benklop/esp8266-2-relay-box/project_box_001.png

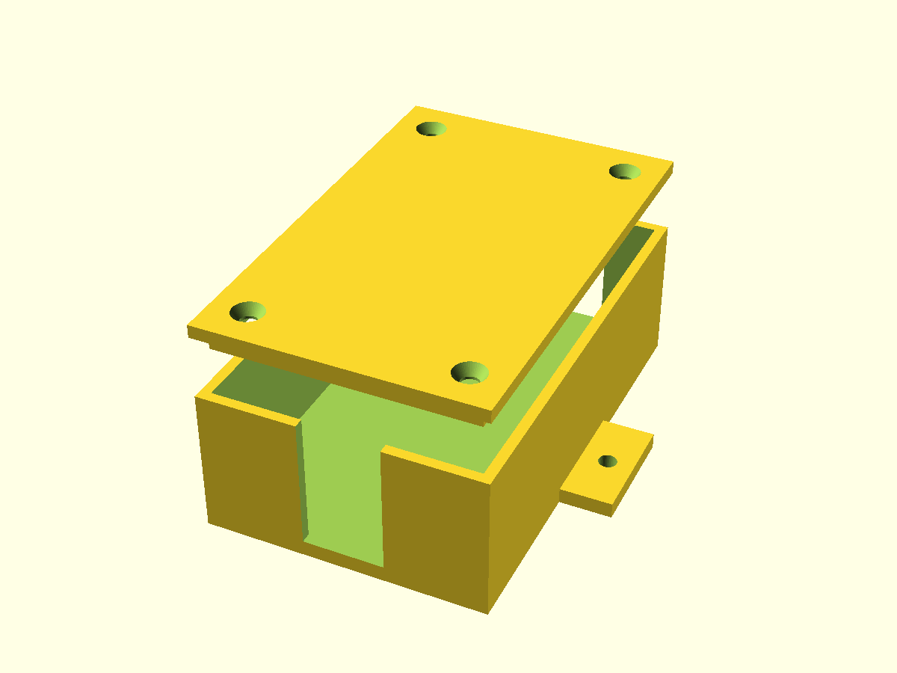
project_box_001.png
