benklop/esp8266-2-relay-box/project_box_001_interior.png

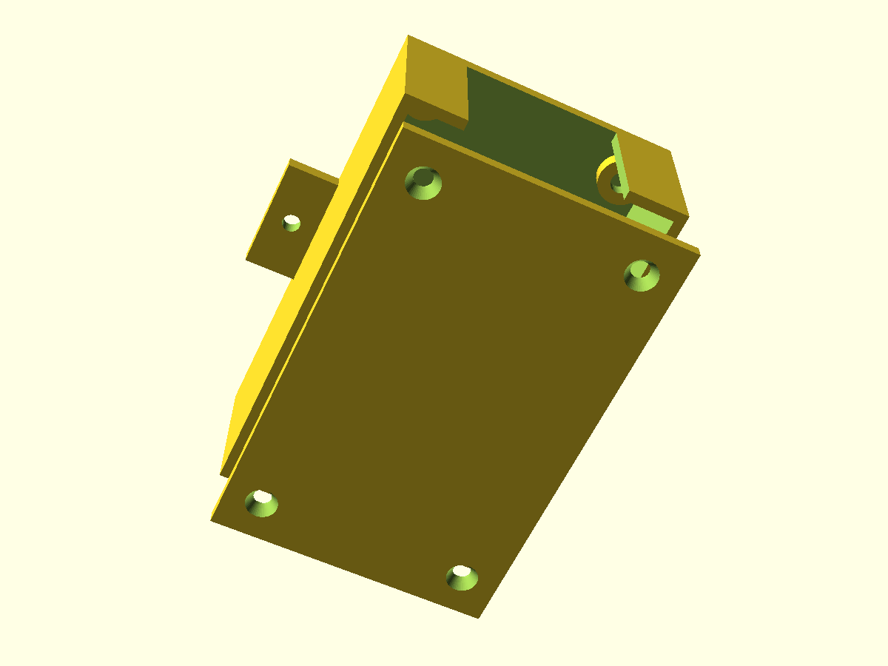
project_box_001_interior.png
