benklop/esp8266-2-relay-box/project_box_002_box.png

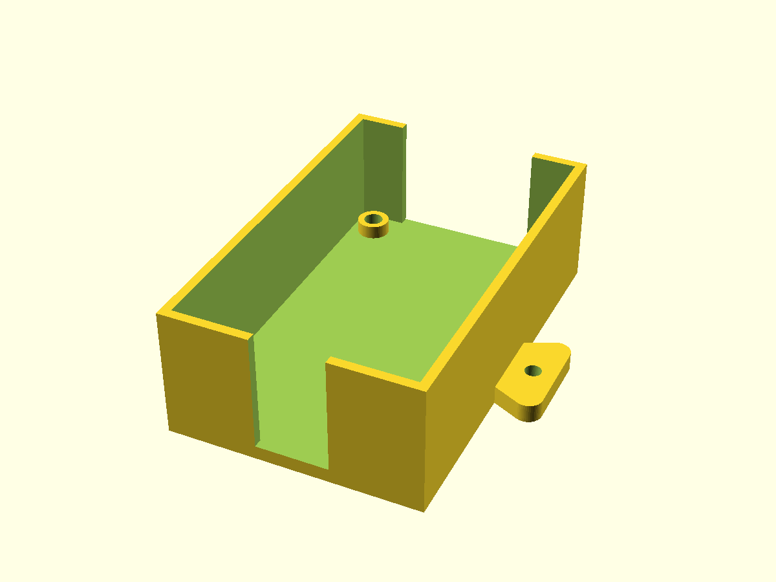
project_box_002_box.png
