benklop/esp8266-2-relay-box/project_box_lid_004.png

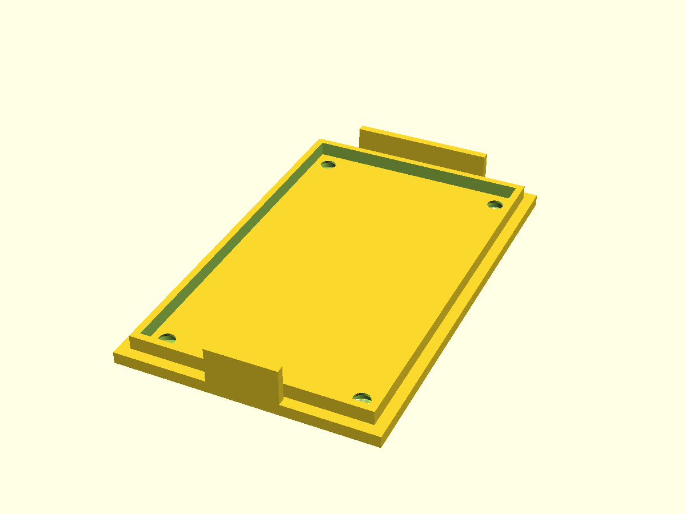
project_box_lid_004.png
